SaberRepublic/Brewboard/images/Diagrams/BrewboardV3_Pixel.png

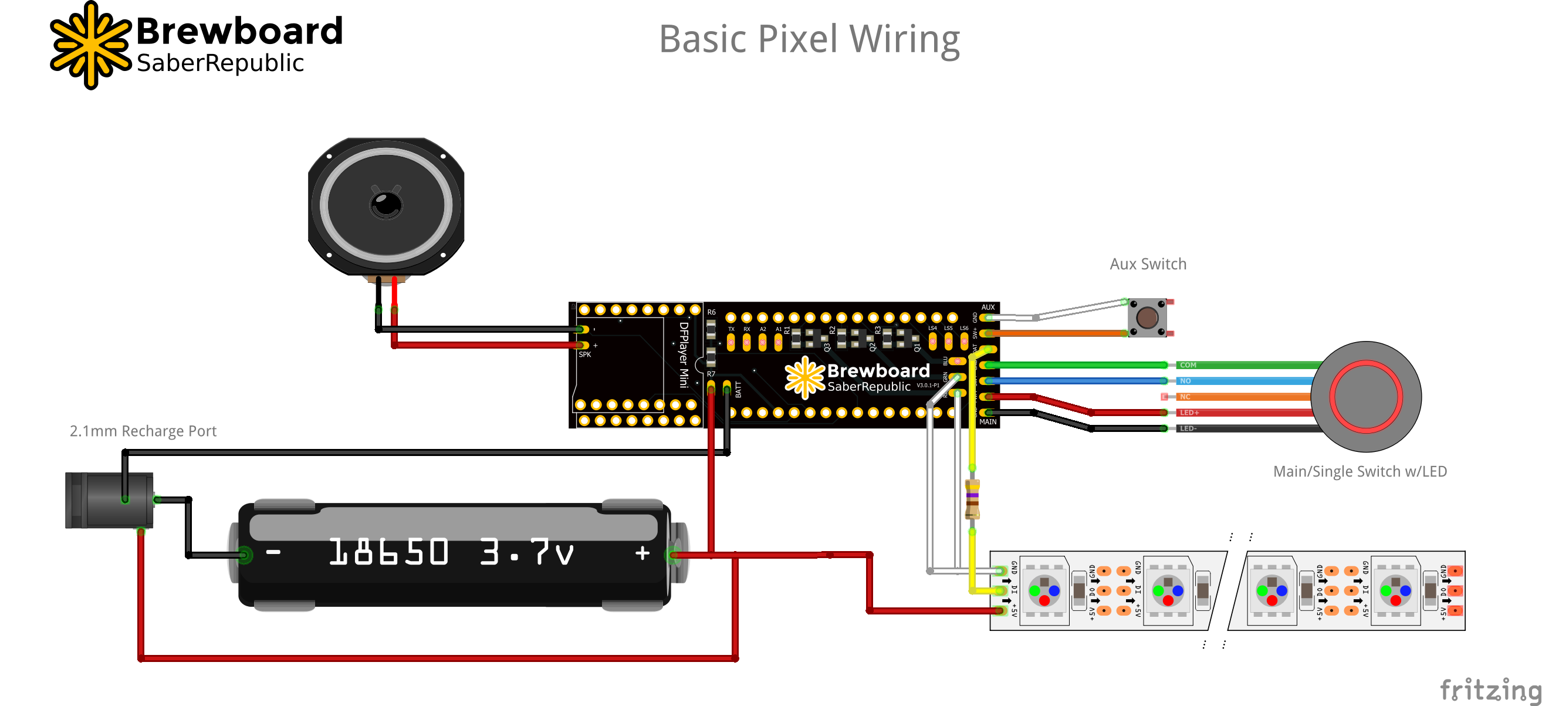
images/Diagrams/BrewboardV3_Pixel.png
