SaberRepublic/Brewboard/images/Diagrams/BrewboardV3_StarLED.png

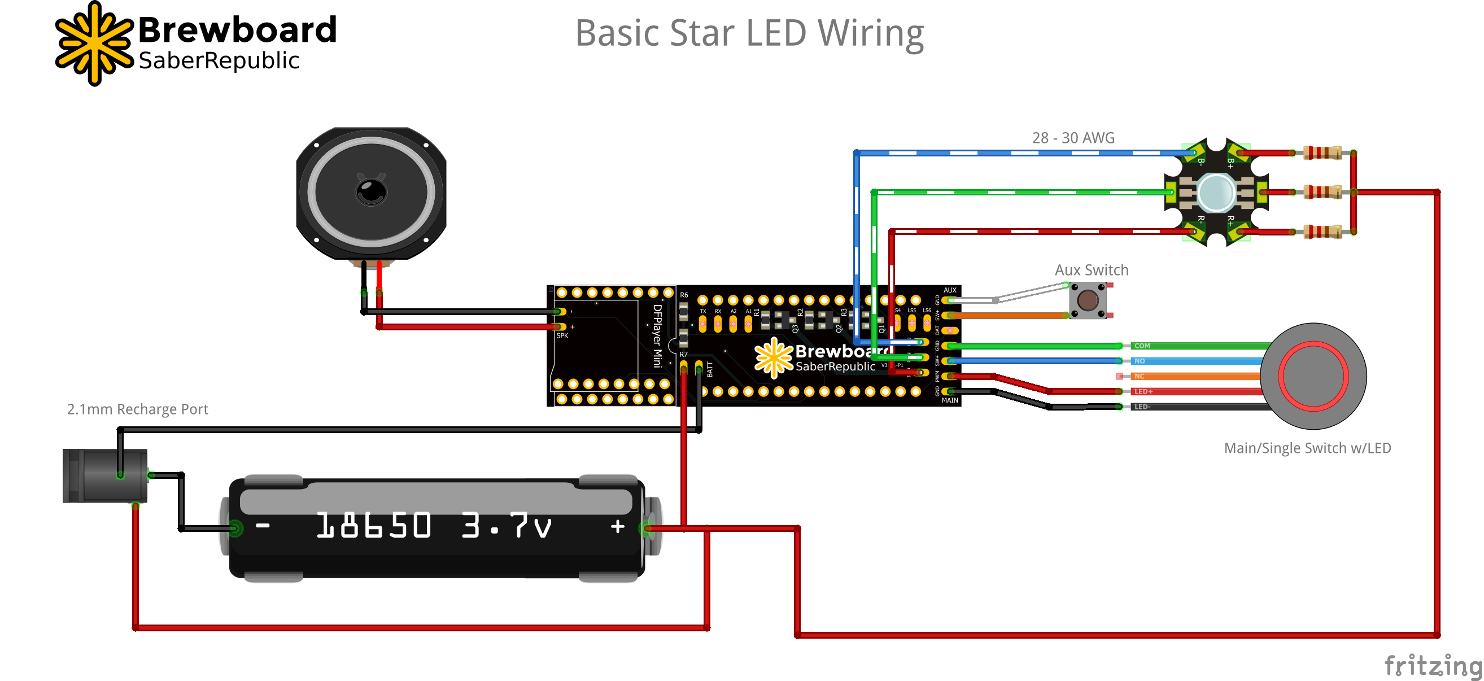
images/Diagrams/BrewboardV3_StarLED.png
