SaberRepublic/Brewboard/images/Diagrams/BrewboardV4_breadboard.png

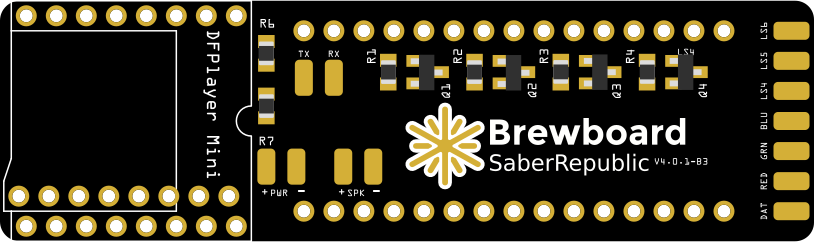
images/Diagrams/BrewboardV4_breadboard.png
