SaberRepublic/Brewboard/images/Diagrams/FritzingBrewboardV3.png

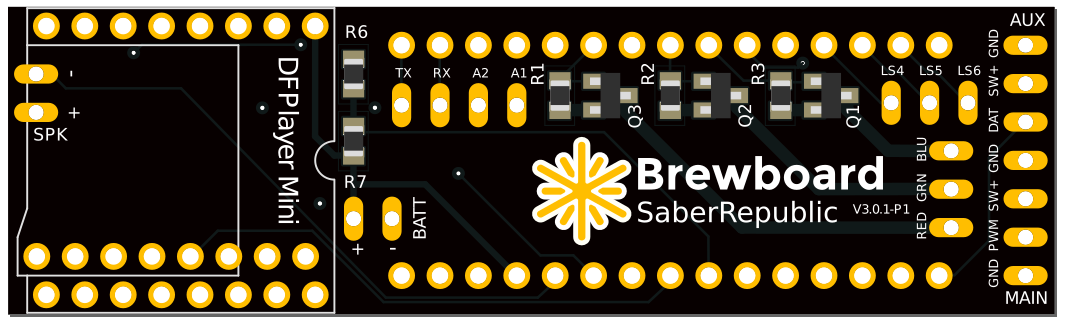
images/Diagrams/FritzingBrewboardV3.png
