SaberRepublic/Brewboard/images/Fritzing/1_FritzingImport.png

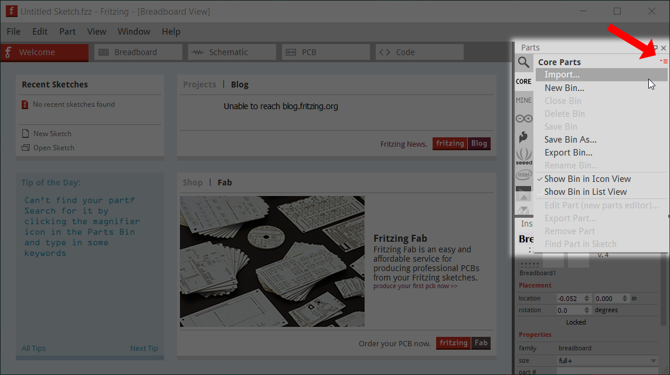
images/Fritzing/1_FritzingImport.png
