SaberRepublic/Brewboard/images/Fritzing/7_UsingTheBoards.png

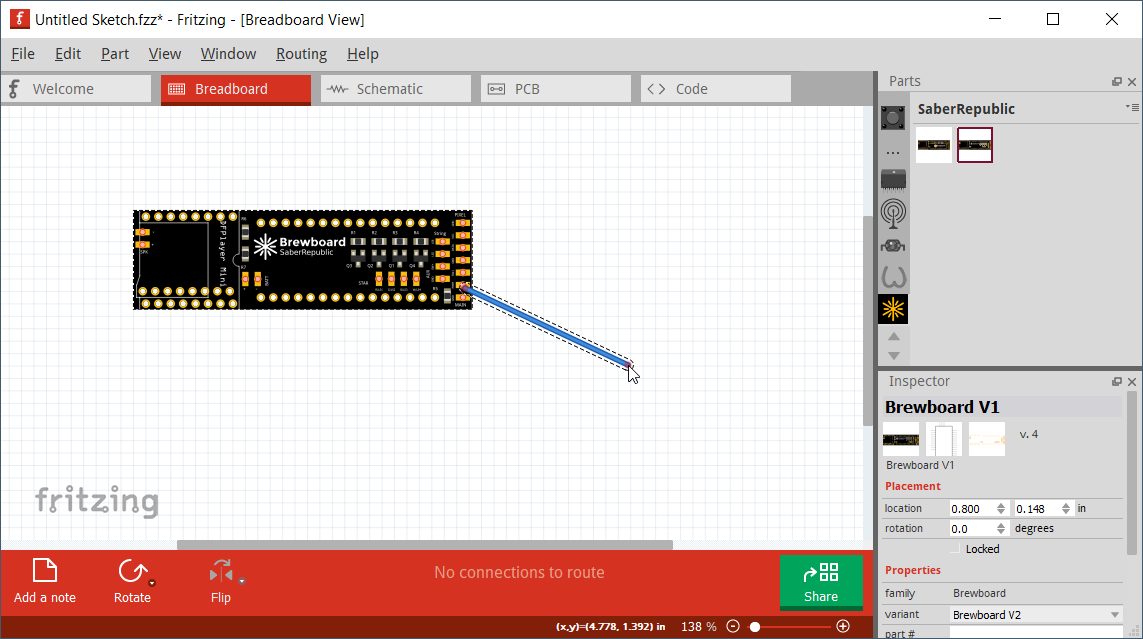
images/Fritzing/7_UsingTheBoards.png
