SaberRepublic/Brewboard/images/Parts/DFPlayerPlacment.png

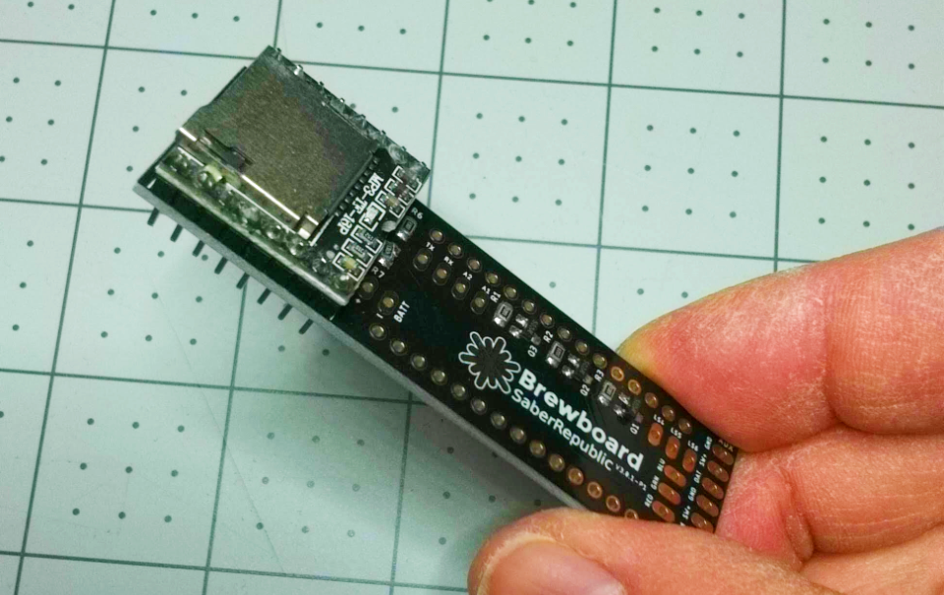
images/Parts/DFPlayerPlacment.png
