SaberRepublic/Brewboard/images/Parts/MPU6050Placement.png

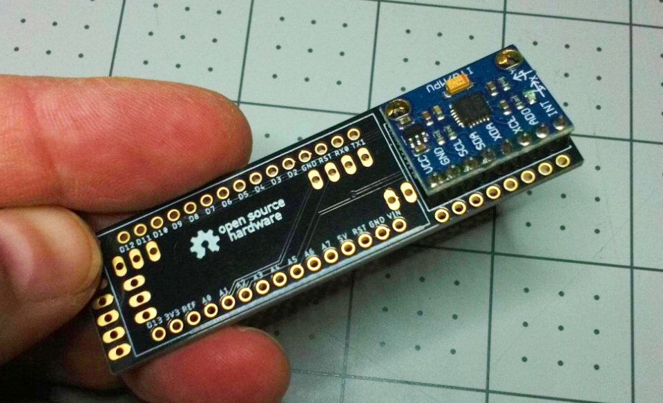
images/Parts/MPU6050Placement.png
