SaberRepublic/Brewboard/images/Parts/NanoPlacement.png

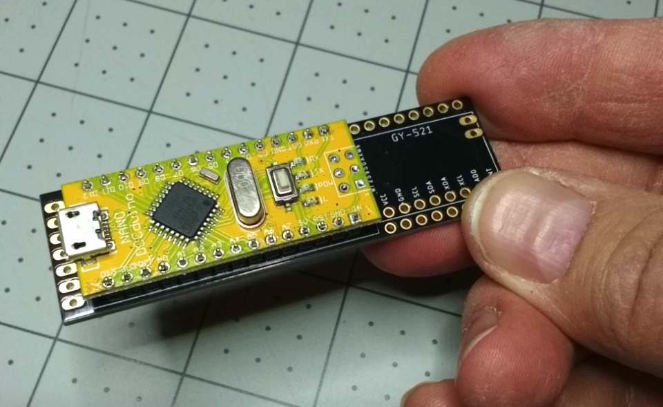
images/Parts/NanoPlacement.png
