SaberRepublic/Brewboard/images/Parts/Parts.png

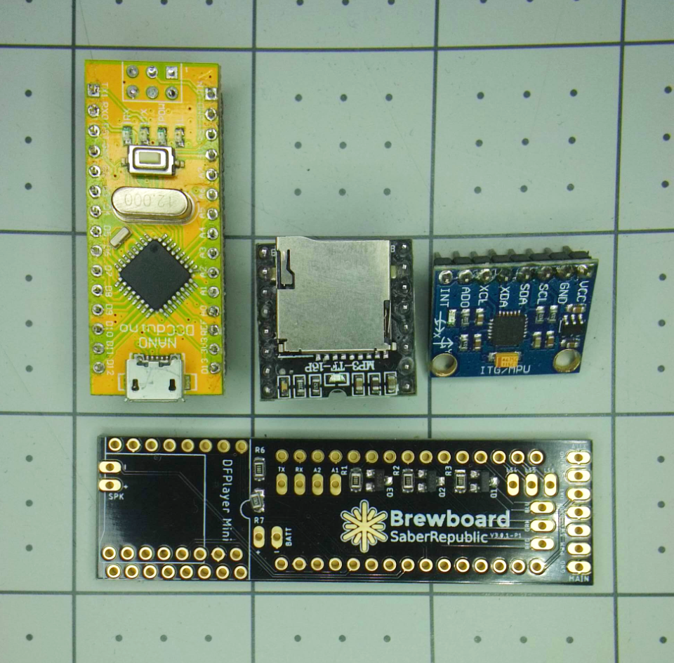
images/Parts/Parts.png
