SaberRepublic/Brewboard/images/Diagrams/BrewboardV3_tp4056 charger_setup.png

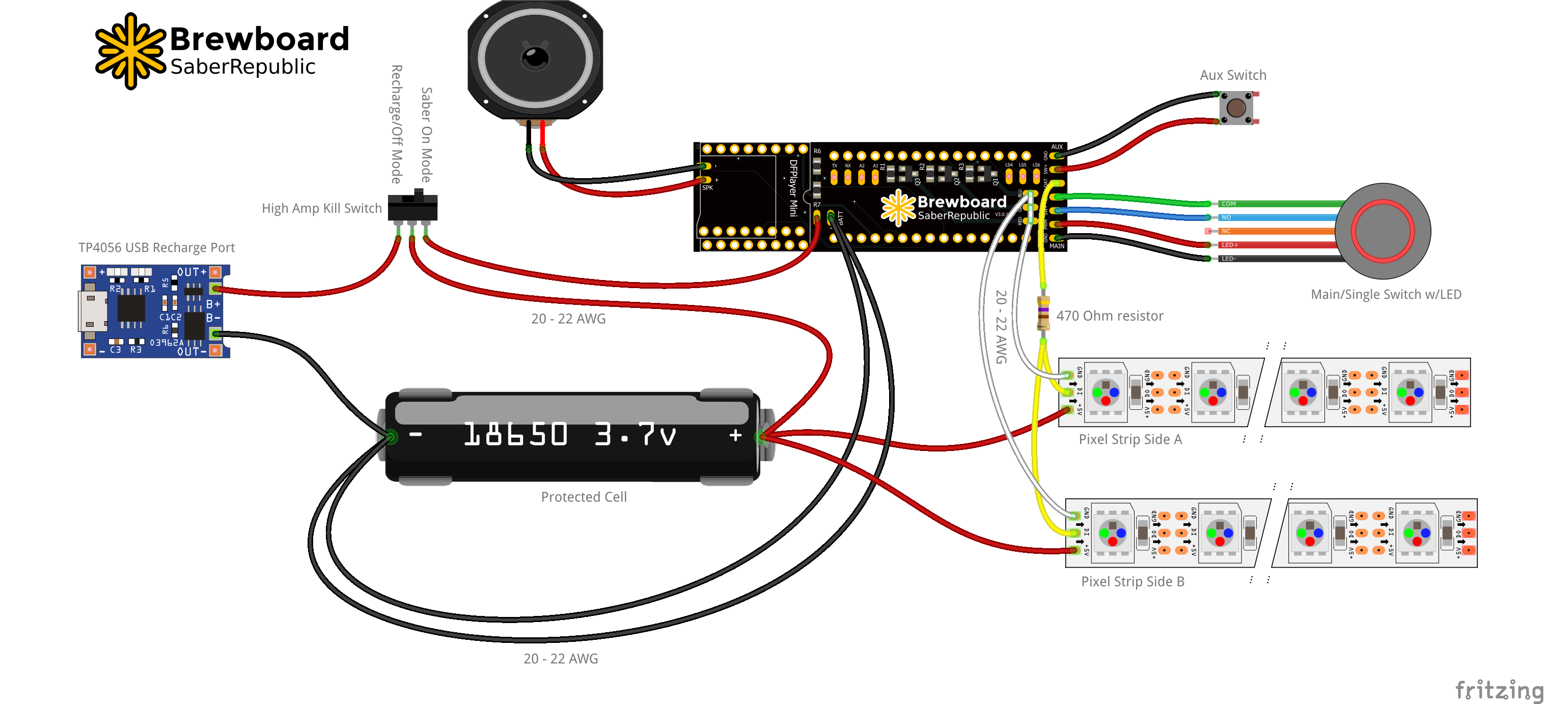
images/Diagrams/BrewboardV3_tp4056 charger_setup.png
